eshazen/retro-25/notes/VFD-Display/Data/IV-6.pdf

www.tube-tester.com

File created by Dieter Waechter

# Dieter’s Nixie Tube Data Archive

This file is a part of Dieter's Nixie- and display tubes data archive

If you have more datasheets, articles, books, pictures or other information about Nixie tubes or other display devices please let me know. Thank you!

Document in this file | Reflector (Sovtek) - IV-6 (ИB-6) original datasheet
Display devices in this document | IV-6 (ИB-6)

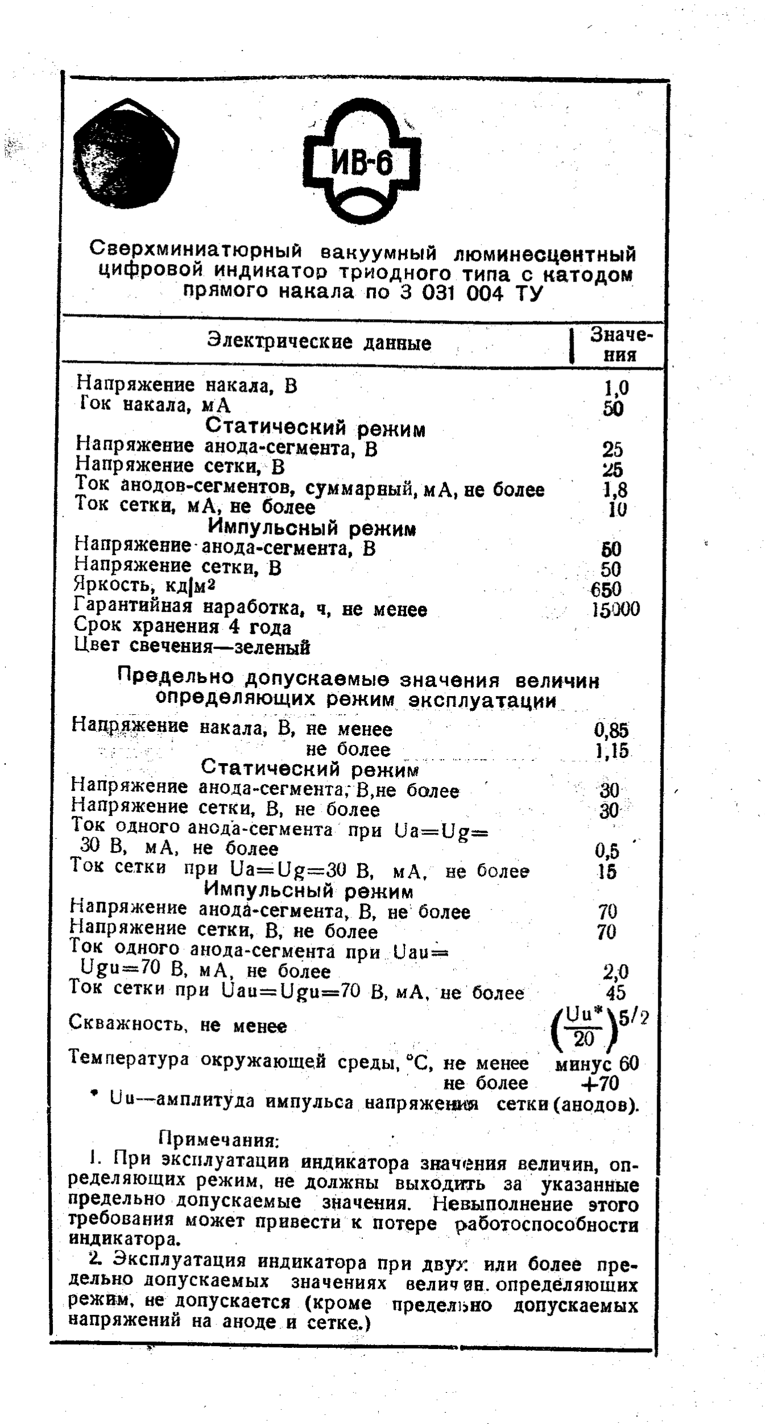
[picture p56: page 2]
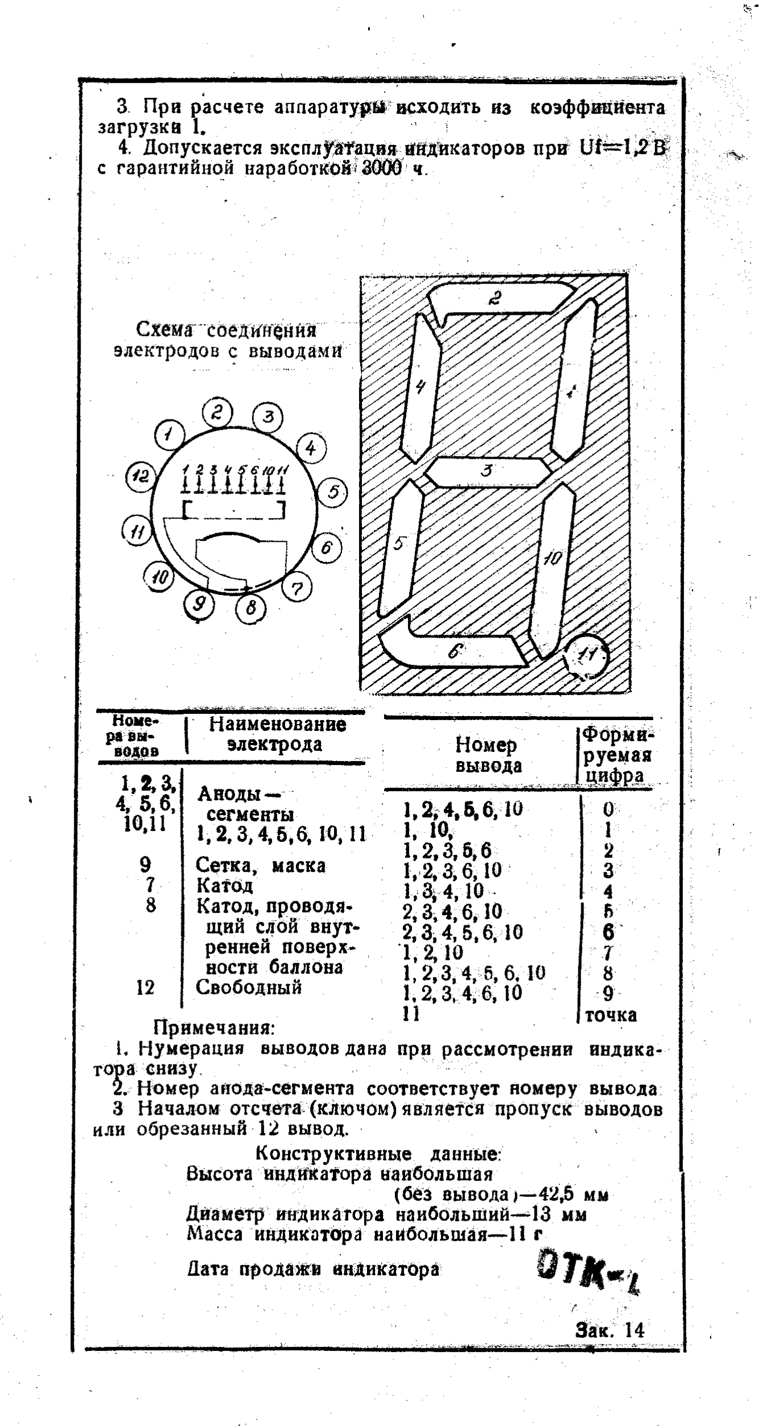
[picture p57: page 3]
