eshazen/retro-25/notes/VFD-Display/Data/in6-data.png

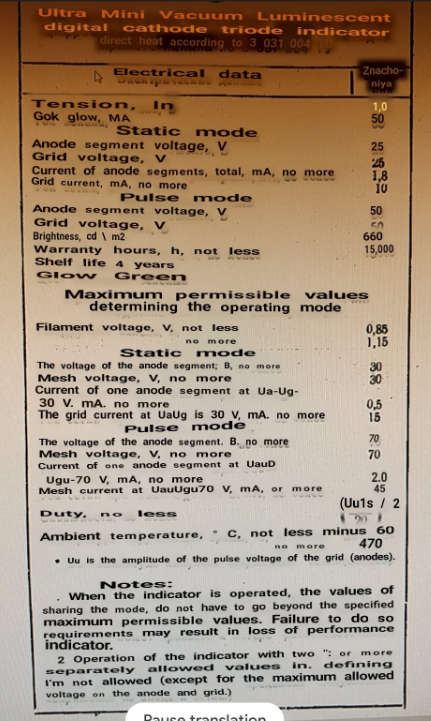
notes/VFD-Display/Data/in6-data.png
