eshazen/retro-25/notes/VFD-Display/Data/japanese-iv-6-breakout.jpg

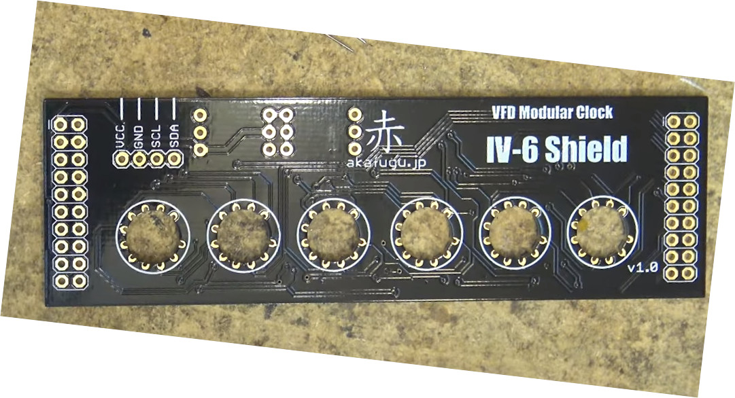
notes/VFD-Display/Data/japanese-iv-6-breakout.jpg
