eshazen/retro-25/notes/VFD-Display/vfd-display-stock-photo.jpg

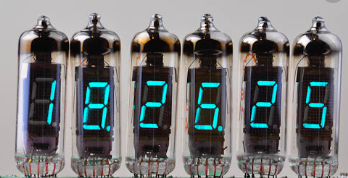
notes/VFD-Display/vfd-display-stock-photo.jpg
