eshazen/retro-25/photos/both800.jpg

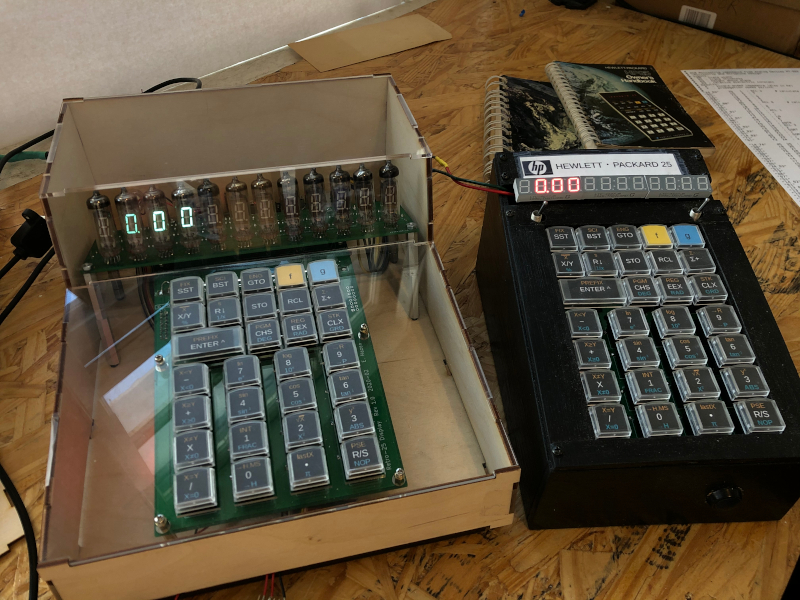
photos/both800.jpg
