eshazen/retro-25/photos/power_supply.jpg

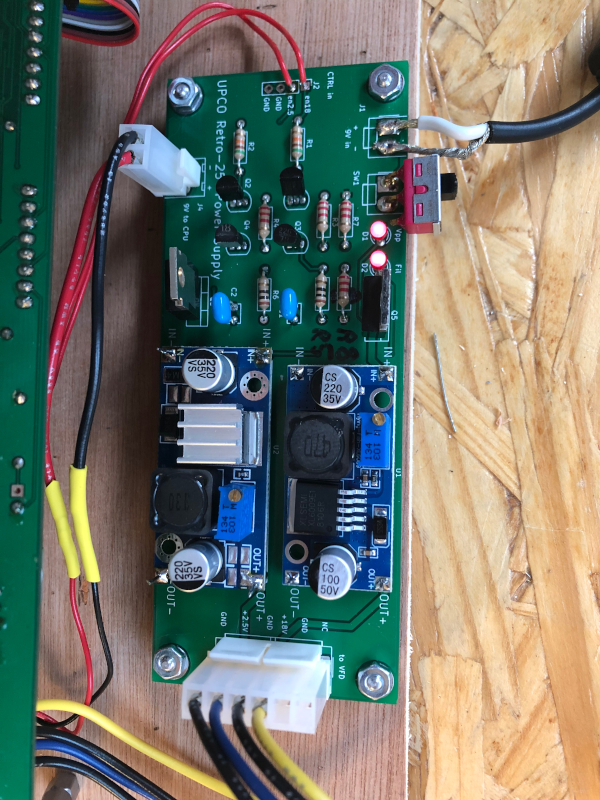
photos/power_supply.jpg
