eshazen/retro-25/talks/HCC2020/figs/display-sch.png

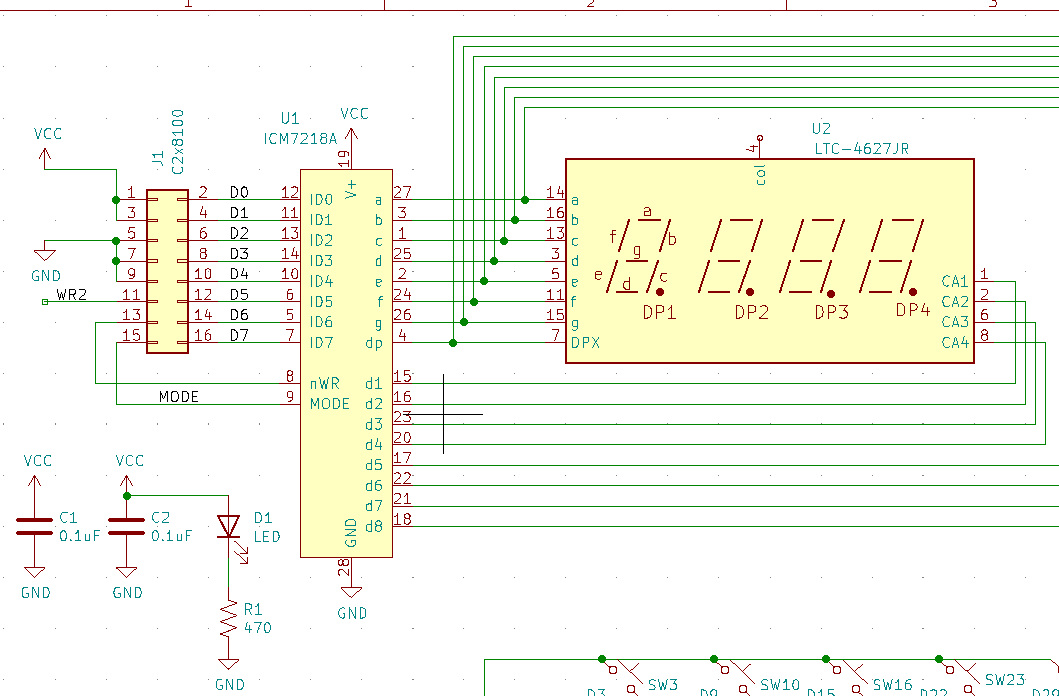
talks/HCC2020/figs/display-sch.png
