eshazen/retro-25/talks/HCC2020/figs/keyboard-sch.png

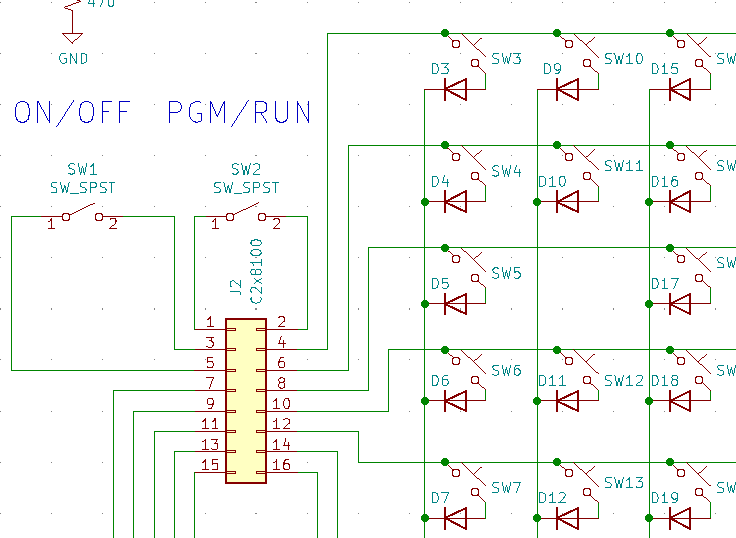
talks/HCC2020/figs/keyboard-sch.png
