eshazen/retro-25/talks/HCC2020/figs/vfd-ps-schem.png

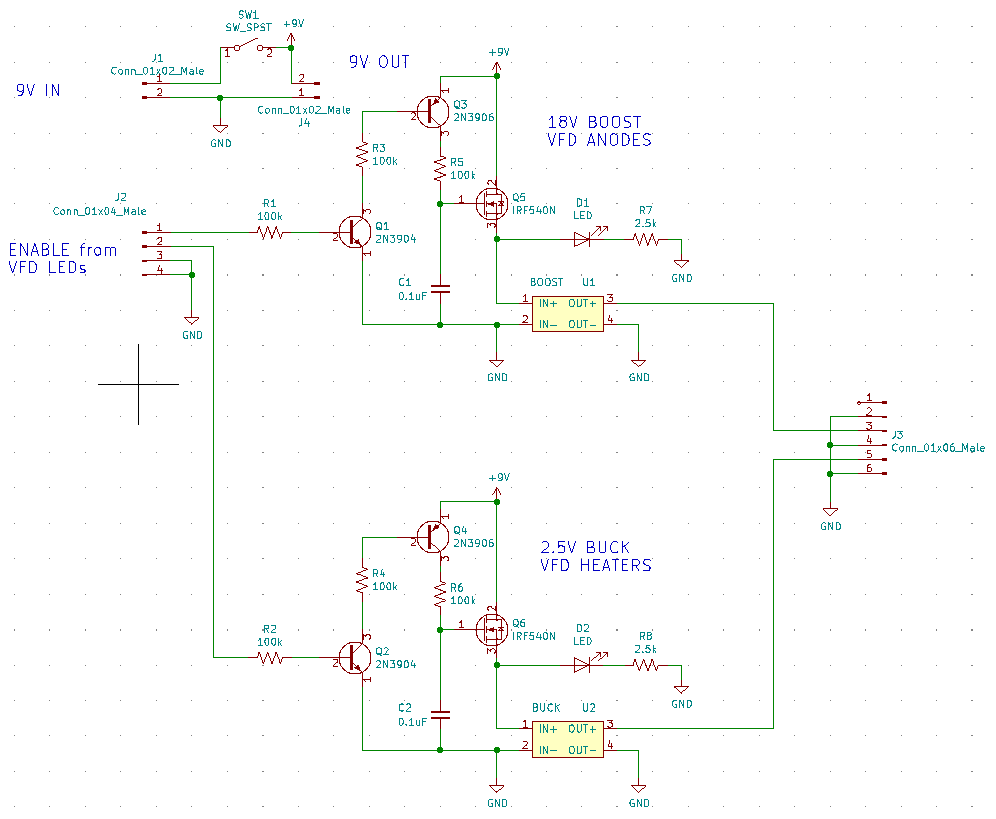
talks/HCC2020/figs/vfd-ps-schem.png
