eshazen/retro-25/enclosure/vfd/front.dxf

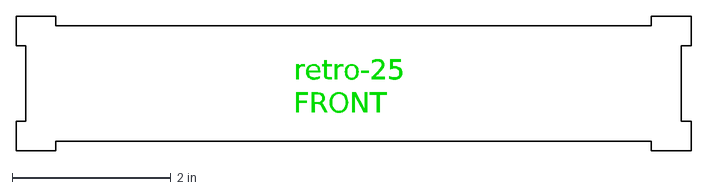
[picture p82: CAD file, 2020-08-07, an earlier design]
enclosure/vfd/front.dxf
retro-25 FRONT
