eshazen/retro-25/enclosure/vfd/top.dxf

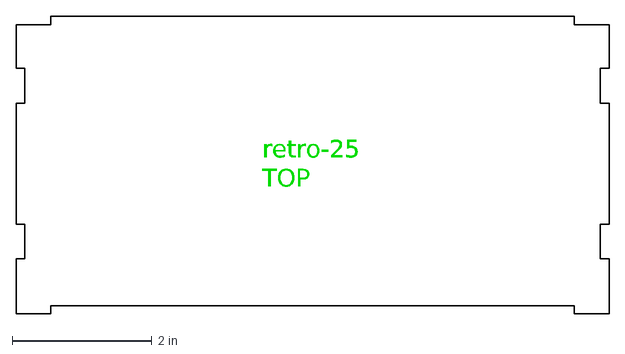
[picture p83: CAD file, 2020-08-07, an earlier design]
enclosure/vfd/top.dxf
retro-25 TOP
