eshazen/retro-25/enclosure/vfd/bottom_plate.dxf

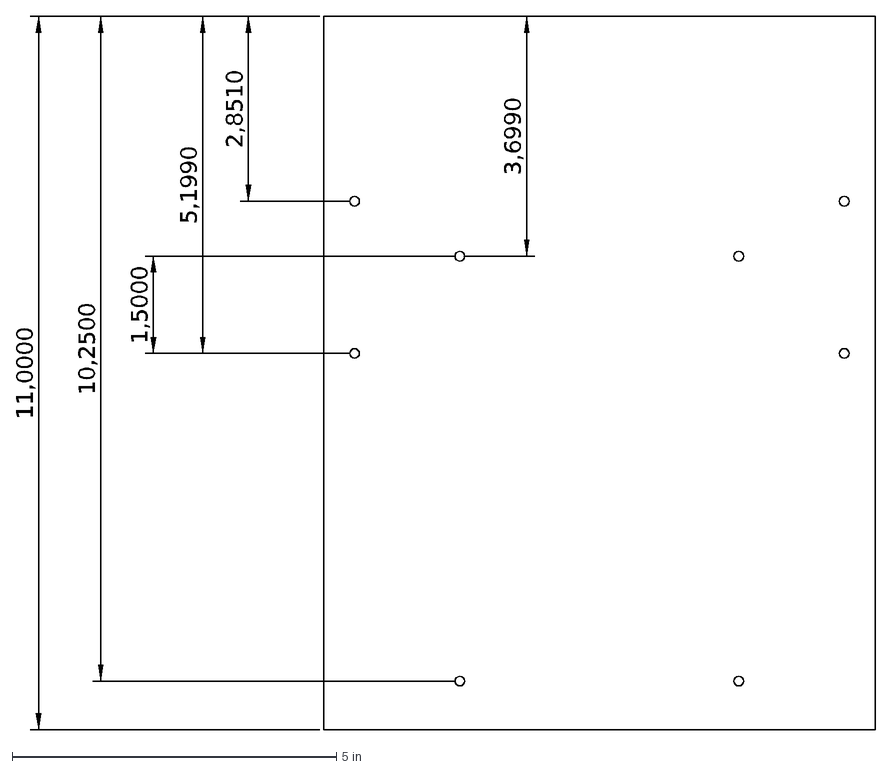
[picture p84: CAD file, 2020-08-06, an earlier design]
enclosure/vfd/bottom_plate.dxf
1,5000
2,8510
5,1990
10,2500
11,0000
3,6990
