eshazen/retro-25/firmware/calc/rom_25.h

#define __ROM25C
static const uint8_t key_map_25c[] = {		// 12 digits (no digit 6) x 3 scan lines
	0x00, 0x73, 0x93, 0xa3, 
	0x00, 0xb3, 0x43, 0xd3,
	0x00, 0x72, 0x92, 0xa2, 
	0x00, 0xb2, 0x42, 0xd3,	//0xd2,
	0x00, 0xb1, 0x41, 0xd1, 
	0x00, 0x00, 0x63, 0x62,
	0x00, 0x00, 0x00, 0x00, 
	0x00, 0xd0, 0x40, 0x61,
	0x00, 0xb0, 0xb4, 0x00, 
	0x00, 0x70, 0x90, 0xa0,
	0x00, 0xd4, 0x44, 0x60,
	0x00, 0x71, 0x91, 0xa1,
};

#ifdef AVR
static const uint8_t rom_25c[] PROGMEM = {
#else
static const uint8_t rom_25c[] = {
#endif
 0x9e, 0x20, 0xa8, 0x20, 0x45, 0x8a, 0x5b, 0x32, 0x68, 0xee, 0x72, 0xdd, 0x06, 0x71, 0x01, 0xd5,
 0x12, 0xf6, 0x7f, 0x46, 0x78, 0x38, 0x30, 0x62, 0xe1, 0x1f, 0xb1, 0x03, 0x36, 0x75, 0x0f, 0xee,
 0x36, 0x8f, 0x78, 0xda, 0x76, 0x74, 0x9b, 0x08, 0x64, 0x21, 0x64, 0x2e, 0x99, 0x23, 0xc2, 0xd5,
 0x01, 0x07, 0x27, 0x62, 0x16, 0xe1, 0x16, 0x15, 0xfb, 0x16, 0x37, 0xee, 0x1d, 0x75, 0xcf, 0x10,
 0x16, 0x8f, 0x71, 0x9f, 0x71, 0x1f, 0xe9, 0xe9, 0x72, 0x26, 0x2b, 0xc2, 0xba, 0x14, 0x42, 0xa3,
 0x27, 0xe0, 0x71, 0x27, 0x5b, 0x27, 0xc6, 0x62, 0xb5, 0xfa, 0x36, 0x13, 0x03, 0xe2, 0x63, 0x7f,
 0xd8, 0x3a, 0x9b, 0x64, 0x75, 0x18, 0x75, 0x60, 0x16, 0x1f, 0x75, 0x00, 0xac, 0x2c, 0x87, 0xf9,
 0x33, 0x1f, 0x00, 0x68, 0x68, 0x18, 0x71, 0x71, 0x84, 0x65, 0x0a, 0xf2, 0x6b, 0xf2, 0x28, 0x00,
 0x46, 0x9c, 0x9a, 0xaa, 0xba, 0xca, 0xda, 0xea, 0xfa, 0x84, 0x77, 0x23, 0x12, 0x61, 0x87, 0x07,
 0x35, 0x37, 0x76, 0x95, 0xf8, 0xa5, 0xf8, 0x43, 0x11, 0x3d, 0x9c, 0xf5, 0xe9, 0x00, 0x9c, 0xac,
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
 0xe8, 0x8a, 0xe8, 0x22, 0xa8, 0x8c, 0xae, 0xaa, 0xa7, 0x9a, 0xae, 0x66, 0x12, 0x11, 0x50, 0x65,
 0x96, 0x0c, 0xaa, 0x96, 0x82, 0x51, 0x08, 0xce, 0xa6, 0x16, 0x45, 0x40, 0x94, 0xc2, 0xaa, 0x8e,
 0xab, 0xa8, 0xab, 0xba, 0x89, 0xa6, 0x0e, 0xae, 0xac, 0xae, 0xca, 0x80, 0xae, 0xc0, 0x00, 0x00,
};
